arxwtf/2024_PiezoPreamp3/ltspice/noise-opamp.png

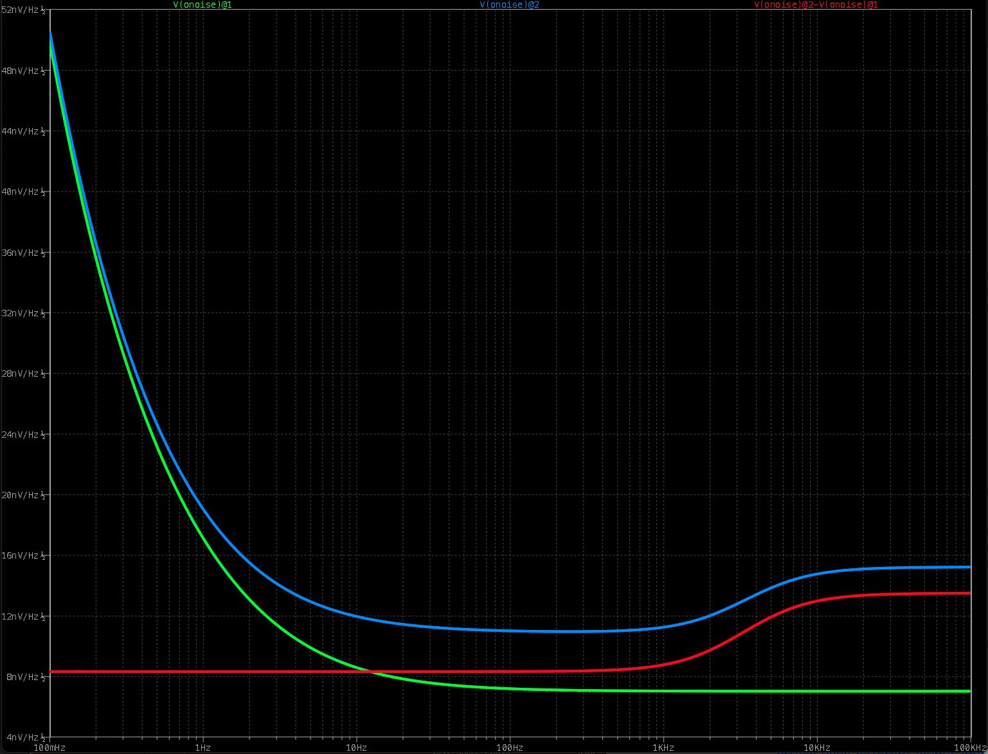
ltspice/noise-opamp.png
