arxwtf/2024_PiezoPreamp3/ltspice/simulation-battery_indicator.png

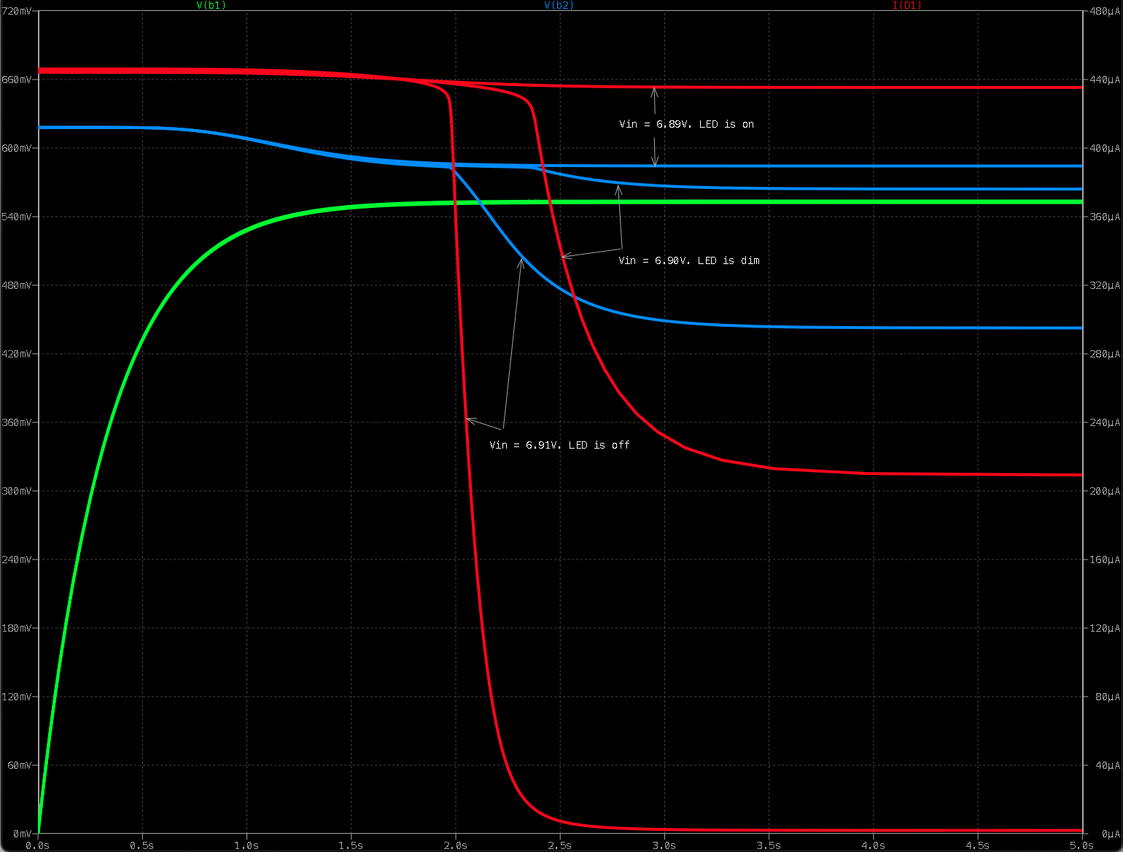
ltspice/simulation-battery_indicator.png
