arxwtf/2024_PiezoPreamp3/ltspice/simulation-charge_amp+bax_HPF.png

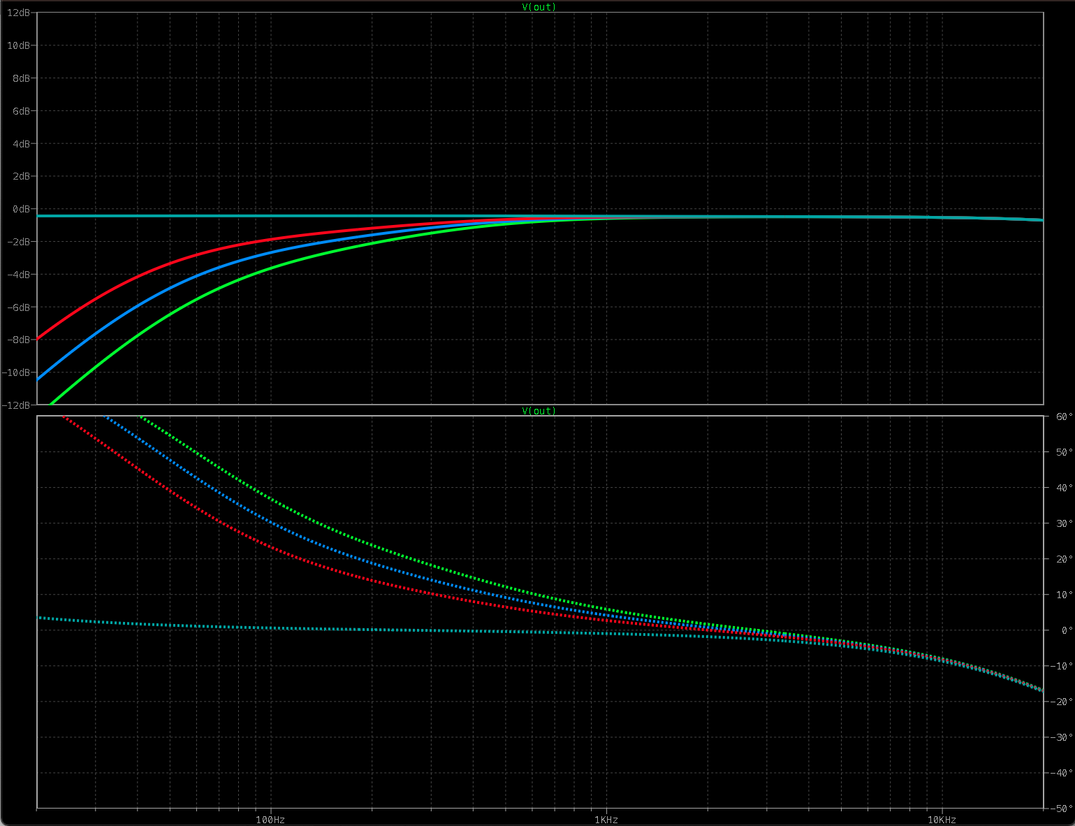
ltspice/simulation-charge_amp+bax_HPF.png
