arxwtf/2024_PiezoPreamp3/ltspice/simulation-charge_amp_only.png

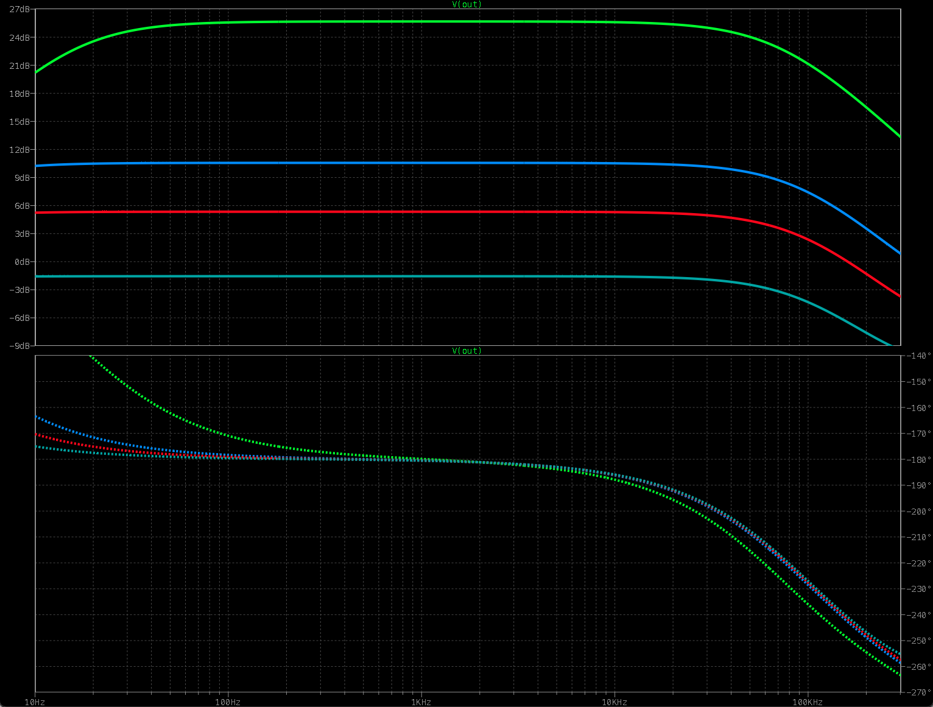
ltspice/simulation-charge_amp_only.png
