arxwtf/2024_PiezoPreamp3/ltspice/simulation-pi_filter.png

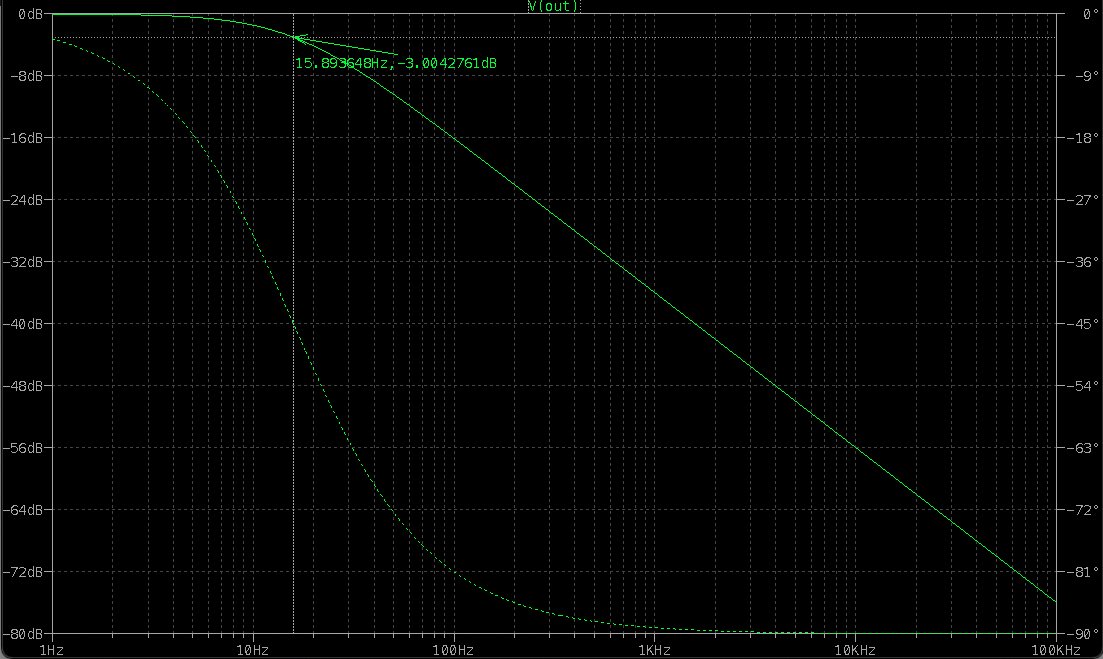
ltspice/simulation-pi_filter.png
