arxwtf/2024_PiezoPreamp3/ltspice/stability-baxandall_only.png

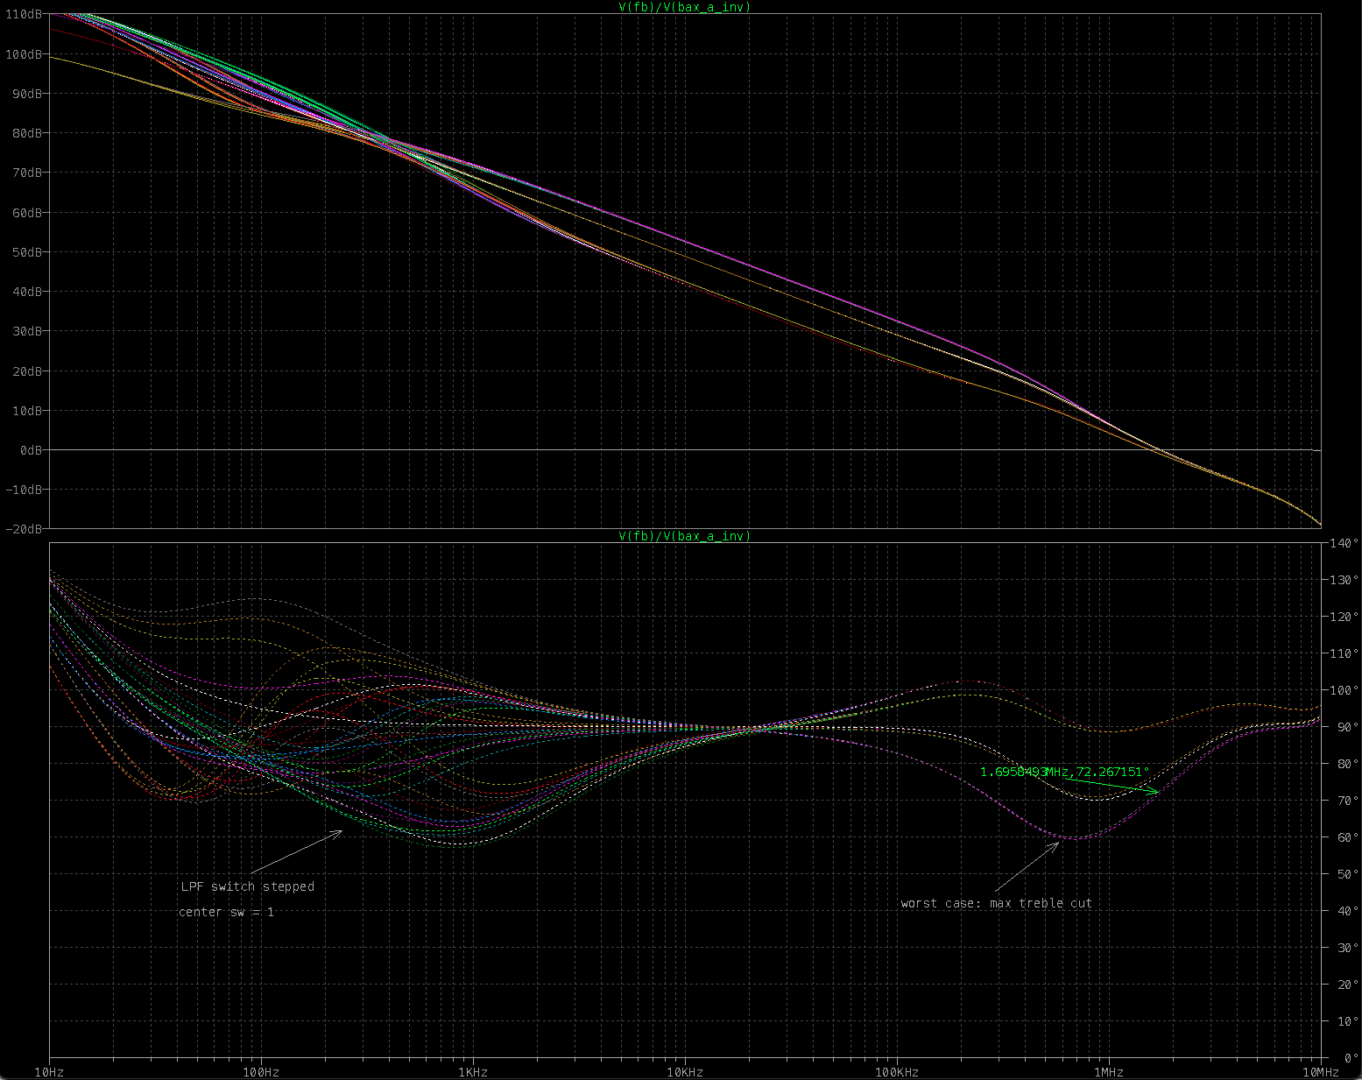
ltspice/stability-baxandall_only.png
