arxwtf/2024_PiezoPreamp3/ltspice/stability-charge_amp+baxandall.png

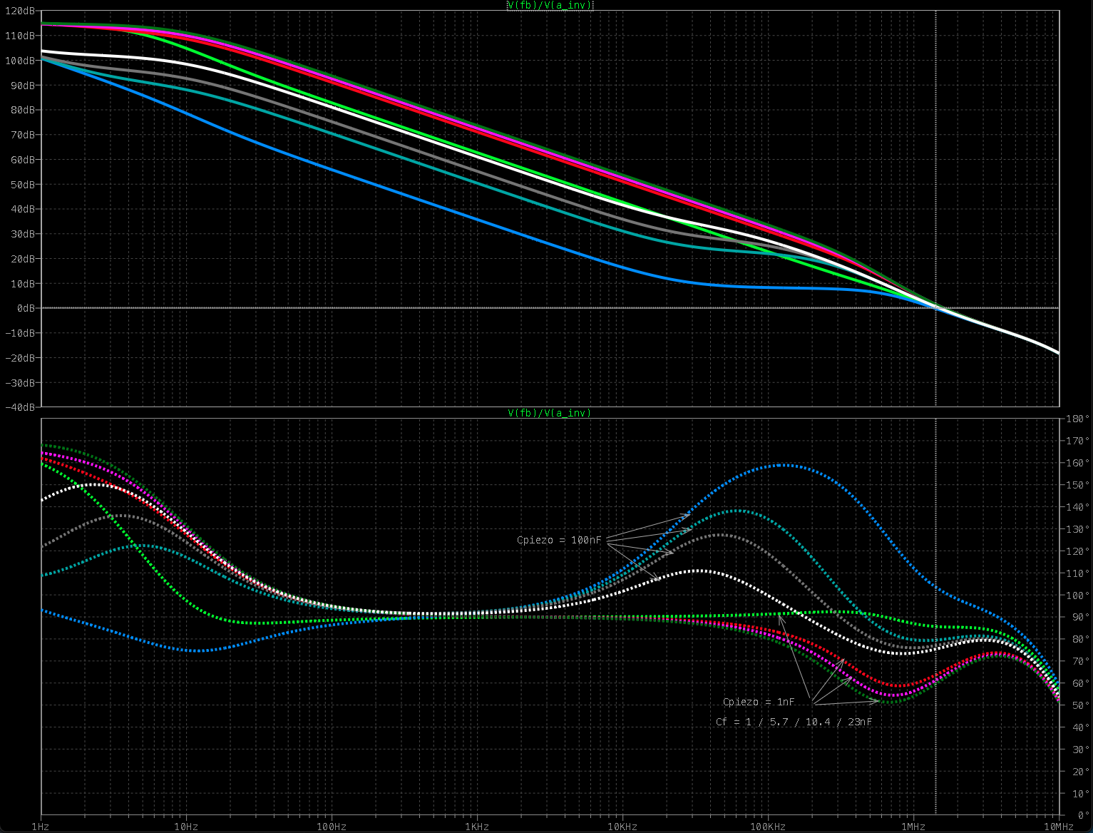
ltspice/stability-charge_amp+baxandall.png
