arxwtf/2024_PiezoPreamp3/ltspice/stability-charge_amp_only.png

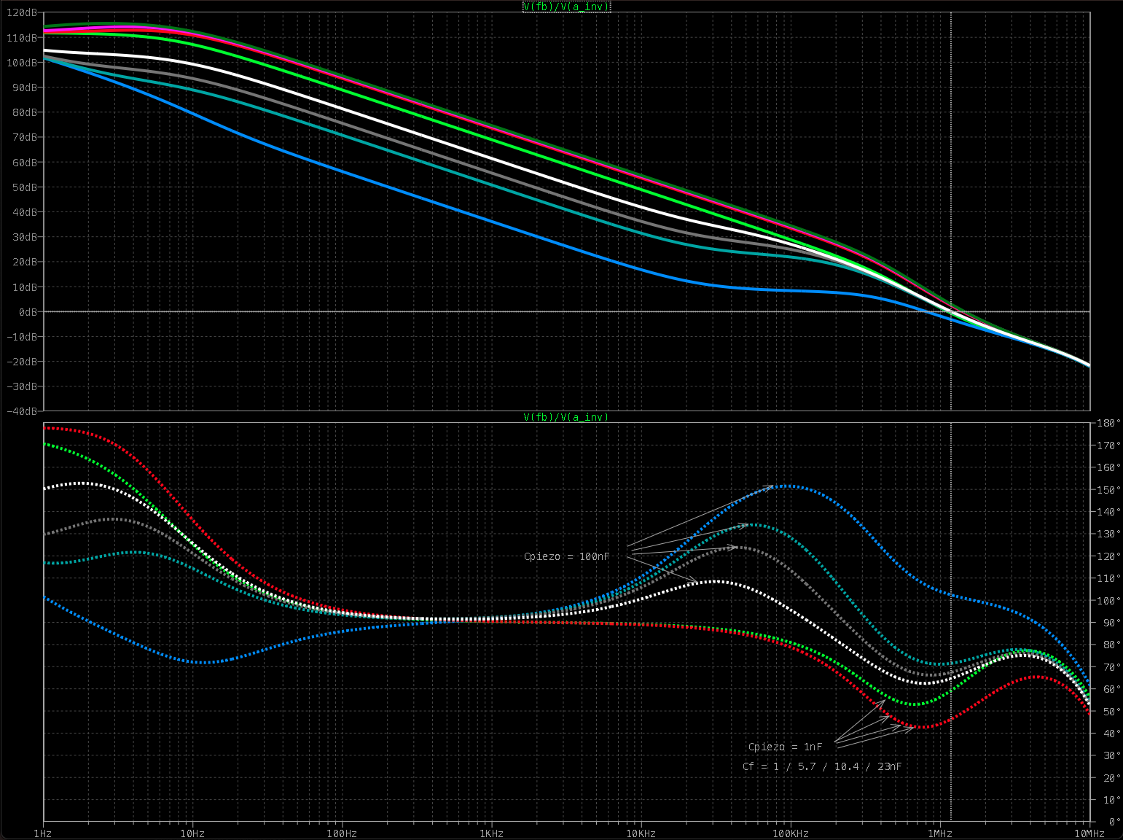
ltspice/stability-charge_amp_only.png
