arxwtf/2024_PiezoPreamp3/production/settings/JLCPCB-Assy_settings_v3_1.png

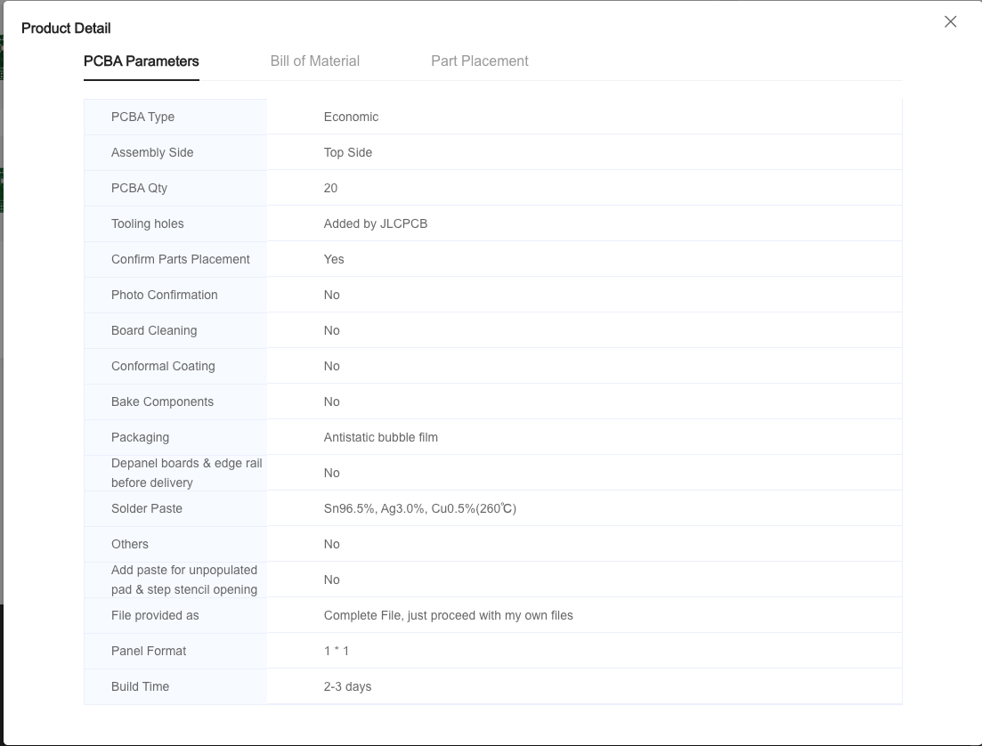
production/settings/JLCPCB-Assy_settings_v3_1.png
