arxwtf/2024_PiezoPreamp3/production/settings/JLCPCB-Fab_settings_v3_0.png

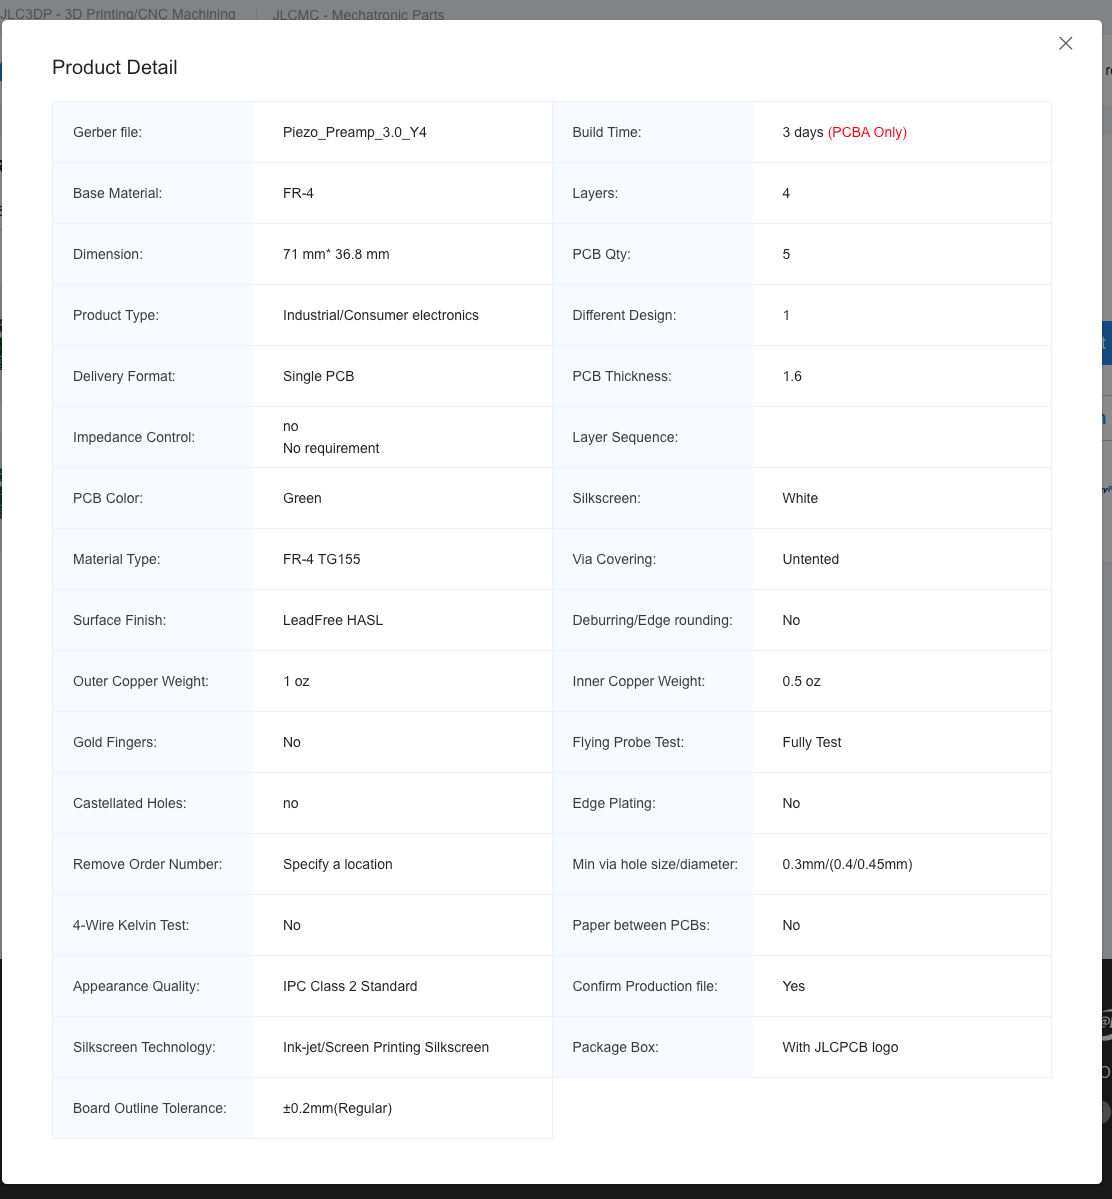
production/settings/JLCPCB-Fab_settings_v3_0.png
