arxwtf/2024_PiezoPreamp3/resources/9V battery indicator Arx.png

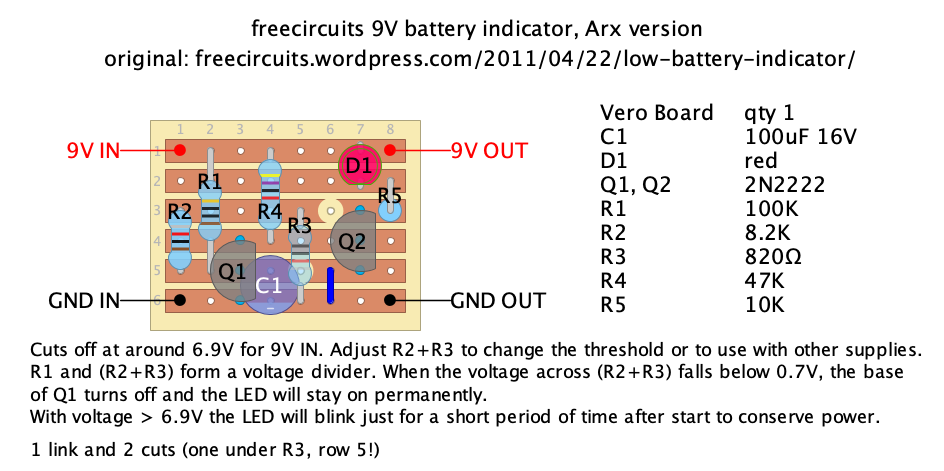
resources/9V battery indicator Arx.png
