arxwtf/2024_PiezoPreamp3/resources/9V battery indicator.png

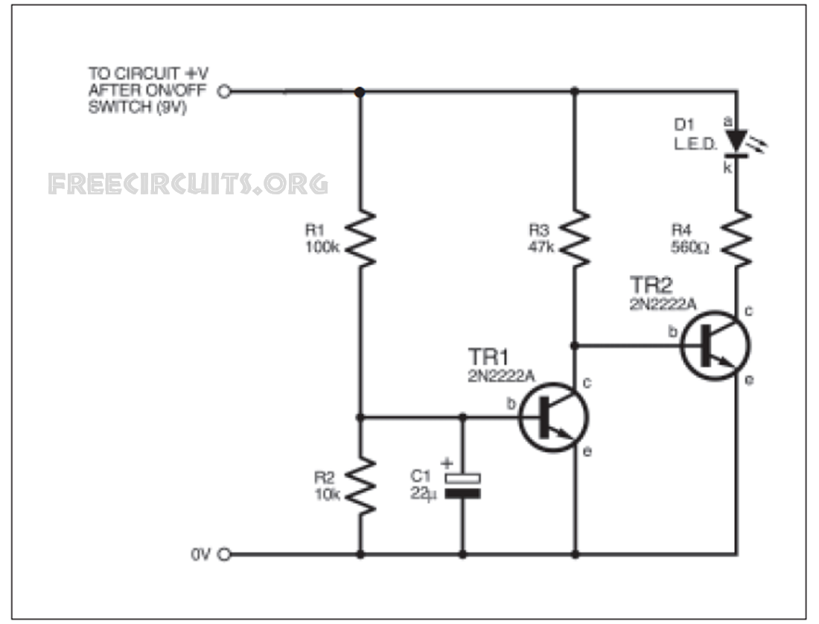
resources/9V battery indicator.png
