arxwtf/2024_PiezoPreamp3/resources/ChargeAmp1.png

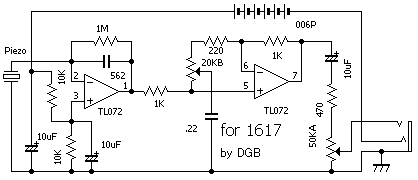
resources/ChargeAmp1.png
