arxwtf/2024_PiezoPreamp3/ltspice/simulation-charge_amp_only.asc

C1: Cap; 10µ
C3: Cap; 100n
C4: Cap; 10µ
Ccable: Cap; 2n
Cf: Cap; {Cf}
Cin: Cap; 660n
Cout: Cap; 100µ
Cpiezo: Cap; {Cpiezo}
R1: Res; 47k
R2: Res; 47k
R3: Res; 200Meg
Rf: Res; {Rf}
Rfix: Res; 1G
Rin: Res; 75
Rout: Res; 60
Rvol: Res; 10k
U1: opamp2; OPAx145
U2: CDSOD323-T12LC
Vbatt: cell; 9; Rser=30
Vpiezo: voltage; SINE(0 100m 1k); AC 1
Named nets: OUT, 0, A_INV, A_OUT, PIEZO, 9V, 4V5, Cp-Cin
.tran 10000u
Rfix is needed, otherwise Cp-Cin
is a floating node - 2 caps in series 
is a problem in LTSpice, as they 
cannot discharge
.inc ./OPAx145.LIB
.op
Piezo Charge Amplifier
.ac dec 100 10 100Meg
.inc ./OPAx134.LIB
.noise V(out) Vpiezo dec 100 0.1 100Meg
.step param Cpiezo list 1n 10n 20n 40n 100n
.step param Cf list 1n 5.7n 10.4n 23n
.step param Rf list 46k 144k 260k 677k 5Meg
piezo capacitances: 1n (very small) - 100n (2x big)
available feedback caps: 1n, 5.7n, 10.4n, 23n
available Rf: 46k, 144k, 260k, 677k, 5Meg
using protective diodes
on A_INV (not used here)
can cause stability issues 
- always verify and place 
them in front of Rin
Rin required for stability.
Will use 2x150R in design.
Rout helps drive output
cable capacitance.
68R in design.
.param Cpiezo 20n
.param Cf 11n
.param Rf 10Meg
.inc ./D20V0L1B2WS.LIB
.measure noise NOISERMS integ V(onoise) from 0.1 to 100Meg
